pozsarzs/mm3d-hw/cad_files/example/example_routing.sch

## KiCad design cad_files/example/example_routing.sch (2019-08-28)

Schematic: example_routing.sch

Parts:
Cs1: Screw_Terminal_01x06
Cs2: Screw_Terminal_01x12
F1, F2, F3, F4, F5: Fuse
J1, J3: Screw_Terminal_01x12
J2: Screw_Terminal_01x02
L1: 24V AC
LA1, LA2, LA3, LA4: Lamp
M1: Motor_AC
R1, R2: Heater
SW1: SW_DPST
SW2: SW_DPST_x2
SW3, SW5: SW_SPST
SW4: SW_SPST_Temperature
U1: DHT22

Notes on the sheet:
MM3D
MM1A
MM2A
Controlled electric heaters
Controlled fluorescent lamps
Magnetic valve solenoid 24V AC
Controlled fan
Thermostat (for operation without MM3D)
Temperature and relative humudity sensor
Water pressure sensor
wall socket 230V AC
emergency light
normal light
Fireman's switch
growing hyphae or mushroom
light on
