pozsarzs/mm3d-hw/cad_files/mm3d/mm3d.sch

## KiCad design cad_files/mm3d/mm3d.sch (2019-08-28)

Schematic: mm3d.sch

Parts:
D1, D2, D3, D4, D5, D6, D7, D8, D9, D10, D11, D12, D13, D14, D15: LED
F1: 2,5A
J1, J3: Screw_Terminal_01x12
J2: CONN_20X2
R1, R2, R3, R4: 4,7k
R5, R6, R7, R8, R9, R10: 330
R11, R12, R13, R14, R15, R16, R17, R18, R19: 220
R101: 4.7k
SW1: SPST
SW2: SWITCH_INV
U1: Level_shifter_4
U2: Level_shifter_I2C
U3: Relay_panel
U101: DHT22

Notes on the sheet:
Outputs
Inputs
ACT (green)
ERR #1-4 (red)
OUT #1-4 (yellow)
Disable relays (red)
GPIO connector
External sensor unit
Rasberry Pi 3 Model B
IN #1-4 (green)
On (green)
+3.3V
S1 +5V
+5V in
GND in
S1 data
S1 GND
IN GND
IN #1
IN #2
IN #3
IN #4
Front panel
Disable relays
+5V
Base panel
